kladogen/AKDrive/Images/IMG_2263.JPG

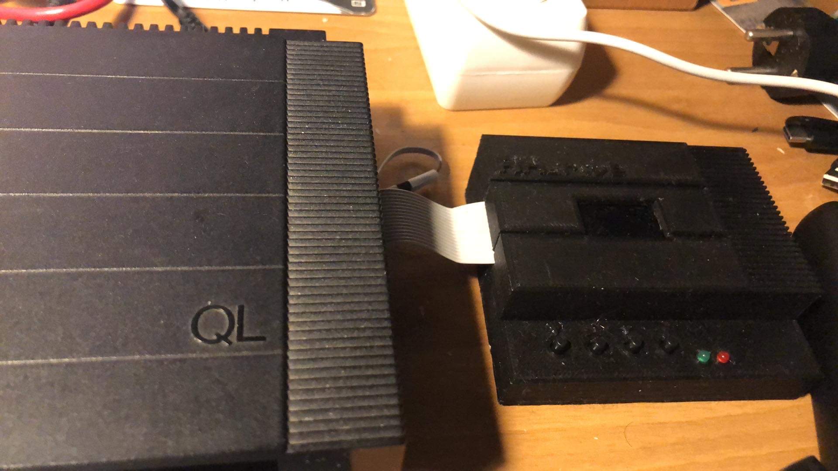
Images/IMG_2263.JPG
