kladogen/AKDrive/Images/IMG_2264.JPG

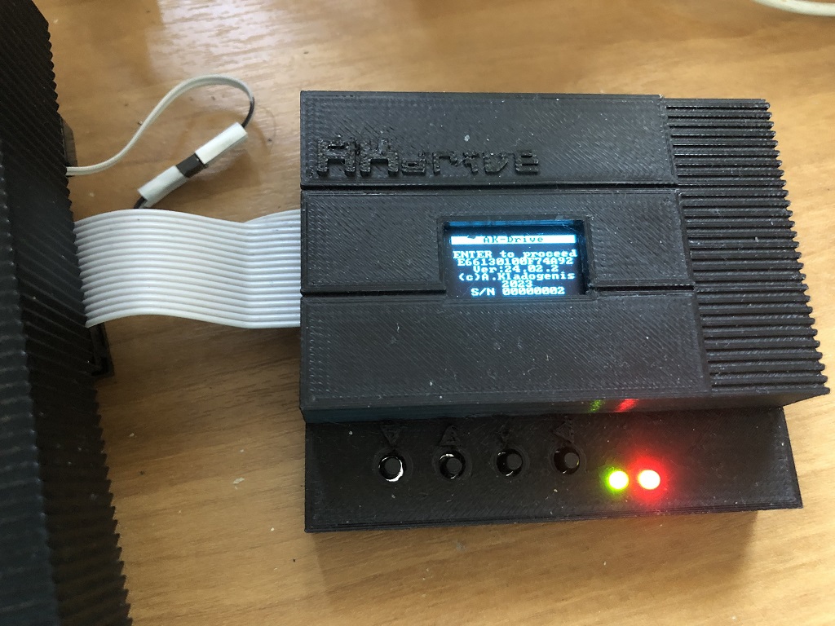
Images/IMG_2264.JPG
