kladogen/AKDrive/Images/IMG_2265.JPG

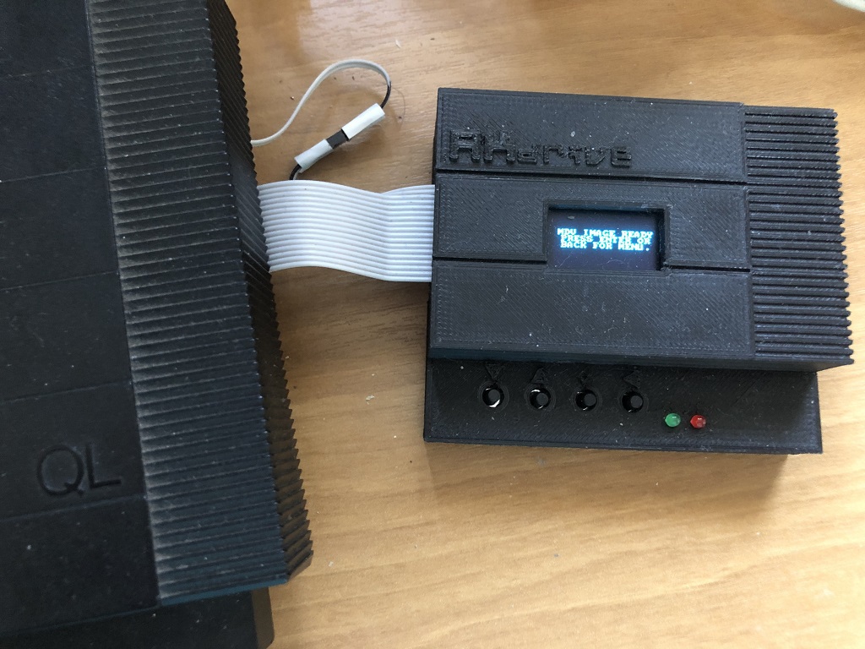
Images/IMG_2265.JPG
