kladogen/AKDrive/Images/IMG_2266.JPG

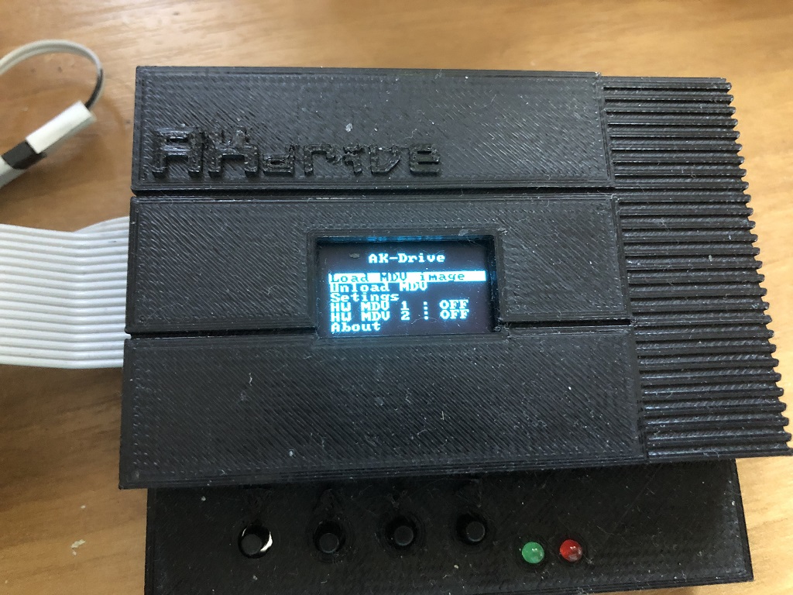
Images/IMG_2266.JPG
