kladogen/AKDrive/Images/IMG_2268.JPG

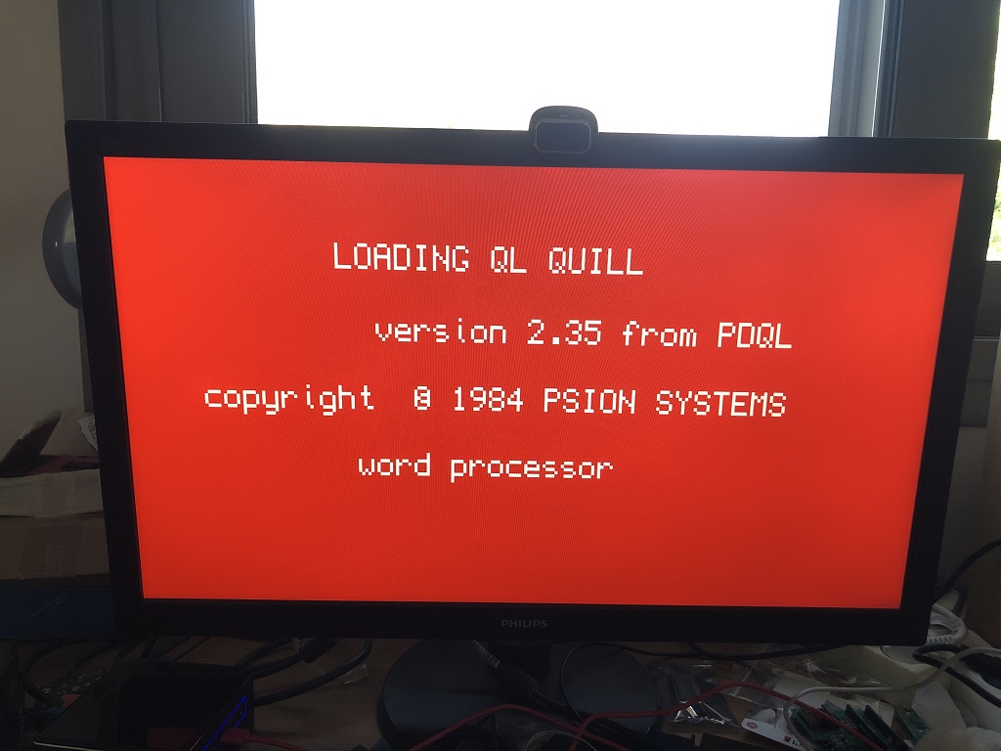
Images/IMG_2268.JPG
